mvx-dev/morphing-airfoil/Airfoils/2414.SLDPRT

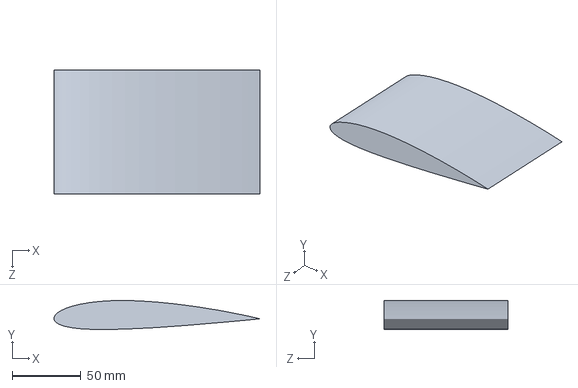
[picture p15: CAD file, 2025-03-19]
Airfoils/2414.SLDPRT
150.0 x 21.2 x 90.0 mm
