mvx-dev/morphing-airfoil/Embedded Systems/Housing/baseplate.SLDPRT

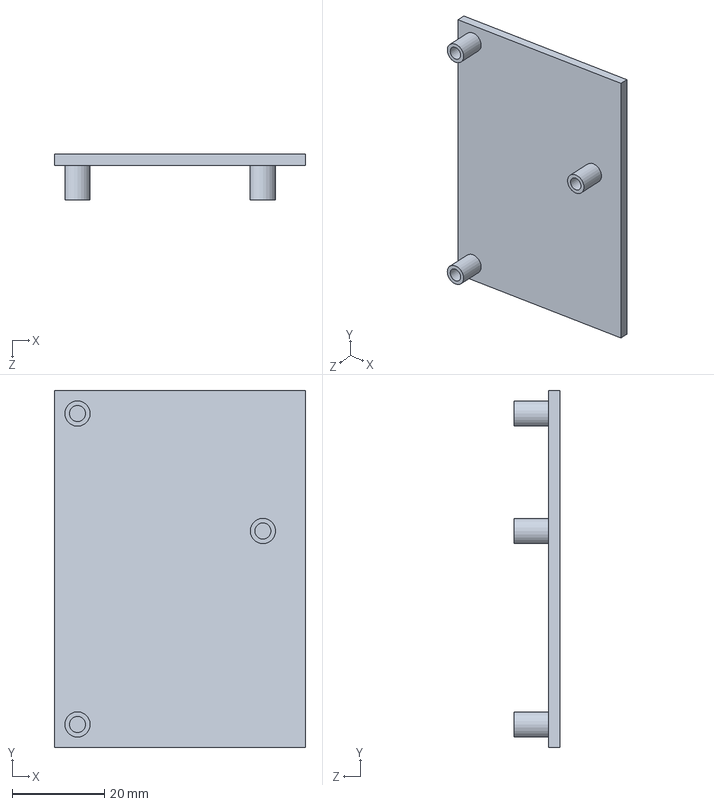
[picture p16: CAD file, 2025-04-11]
Embedded Systems/Housing/baseplate.SLDPRT
54.5 x 77.5 x 10.0 mm
